JarrettR/Globall/Mechanical/R1/DXFs/2 - Motor Pulley.dxf

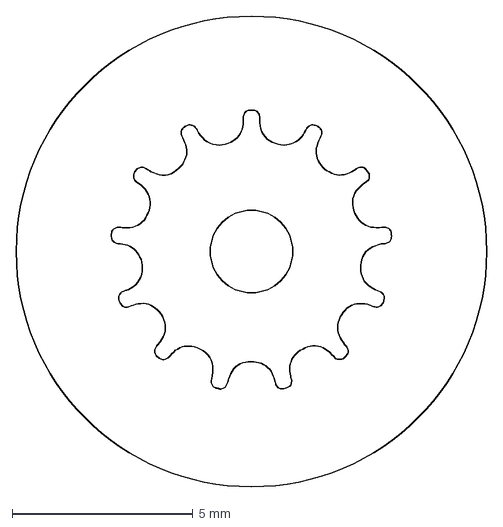
[picture p23: CAD file, 2018-11-27]
Mechanical/R1/DXFs/2 - Motor Pulley.dxf
13.0 x 13.0 mm
